JordanAceto/angelo_modular/pcb_docs/dual_ADSR/dual_ADSR_carrier_board/construction_docs/dual_ADSR_schematic.pdf

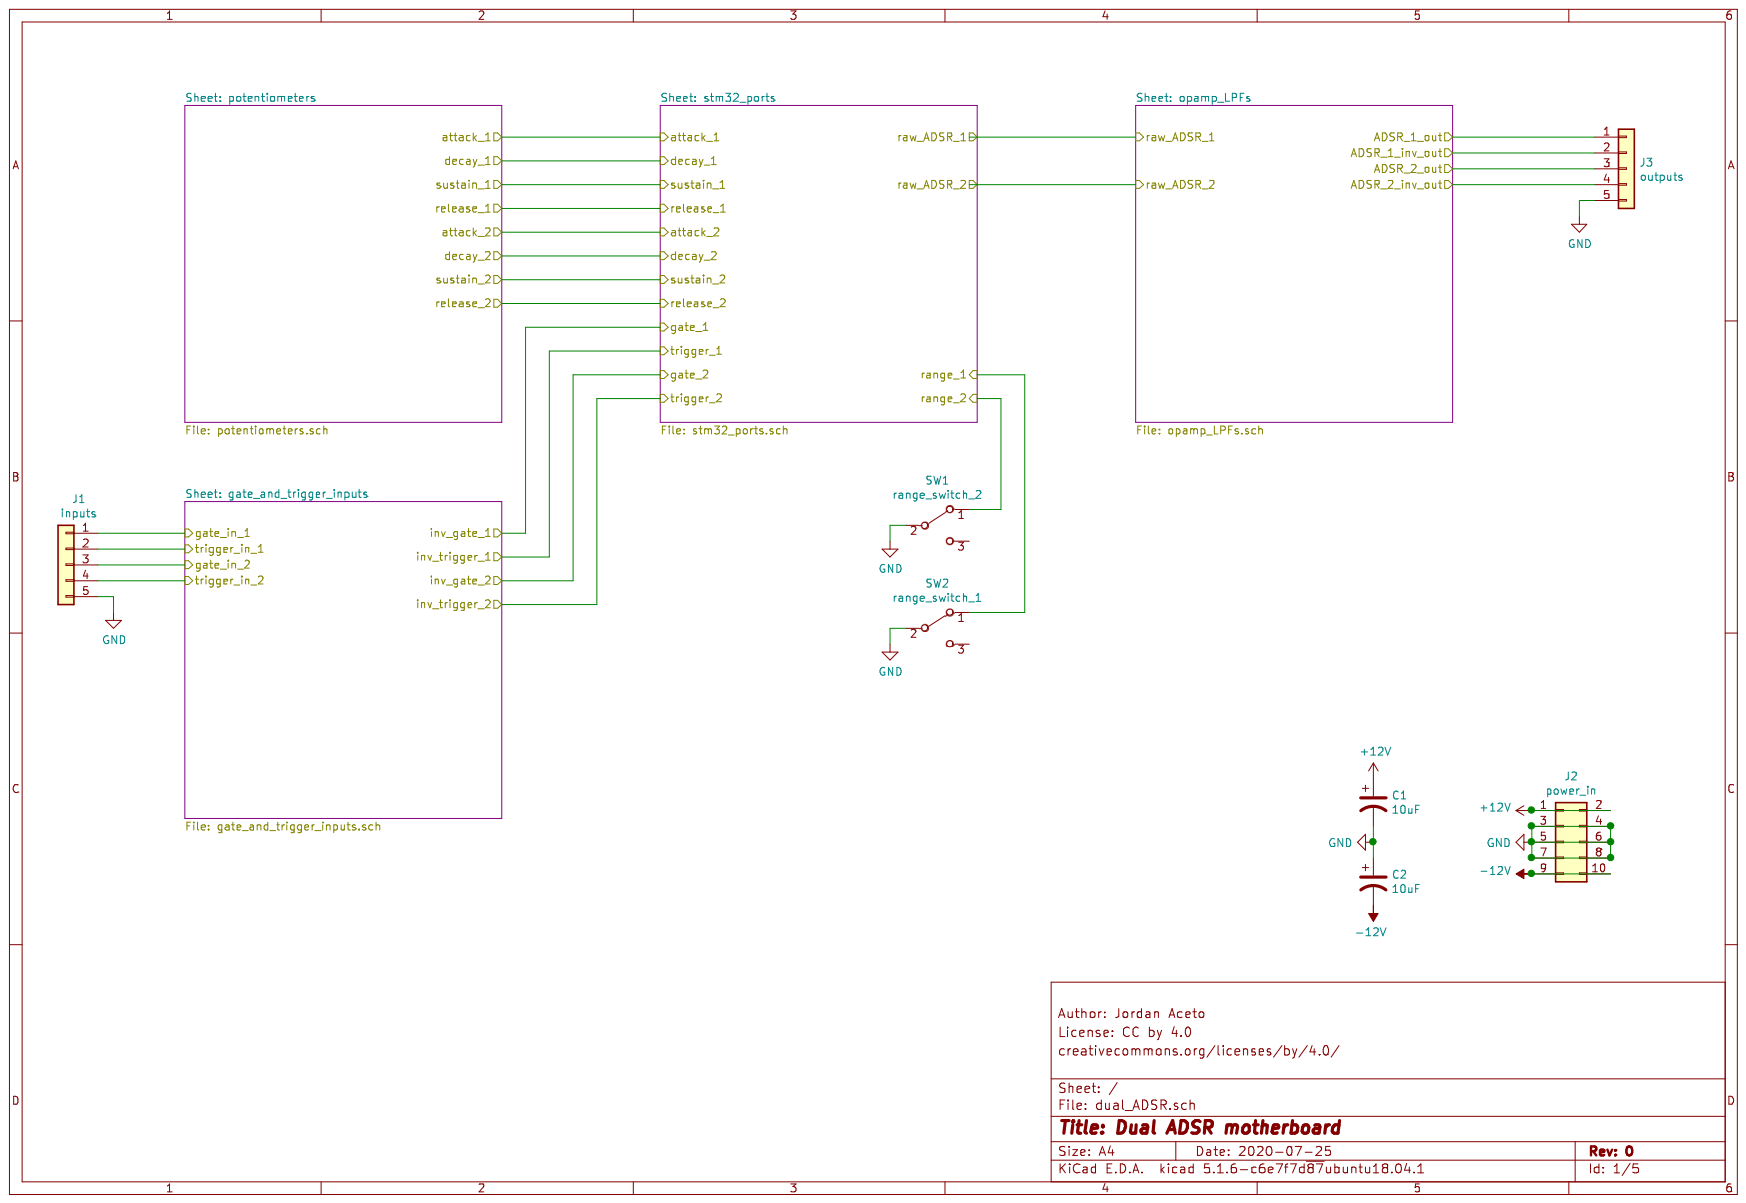
[picture p83: page 1]

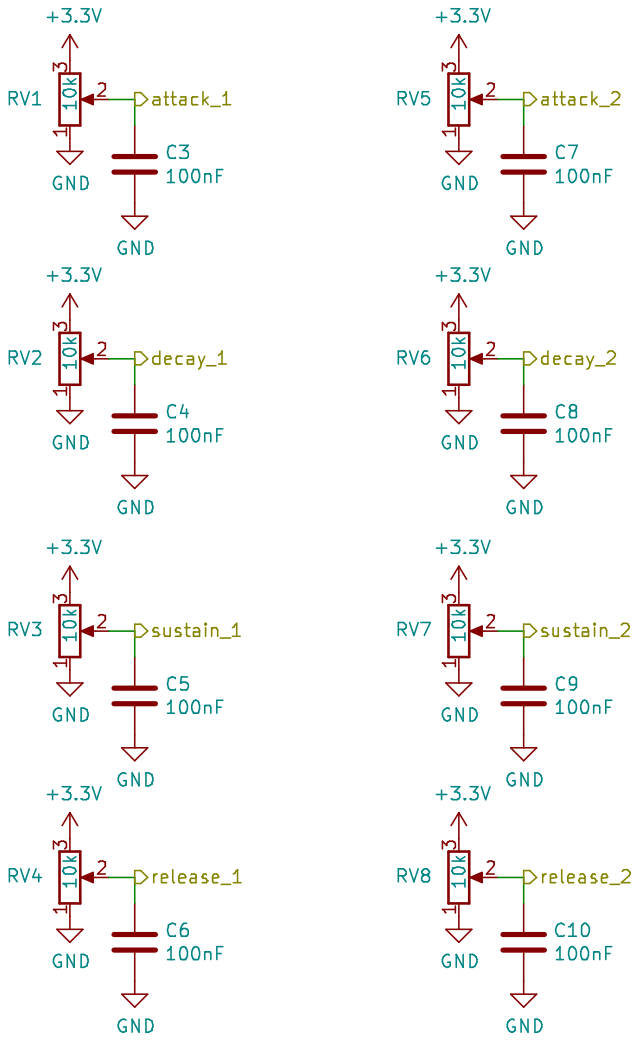
[picture p84: page 2]

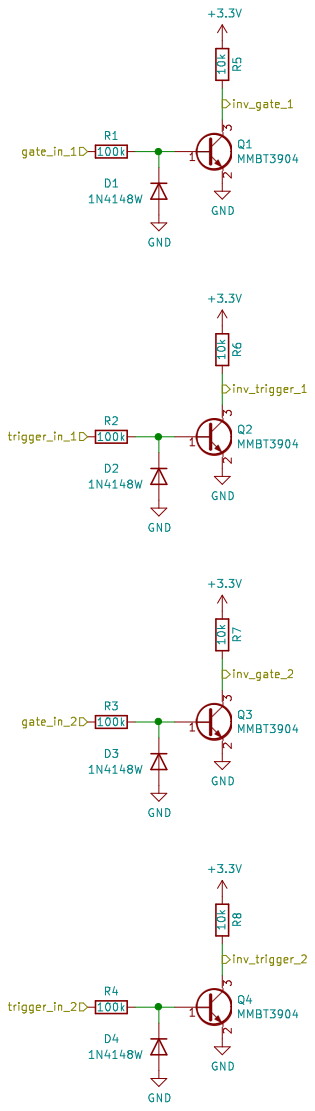
[picture p85: page 3]

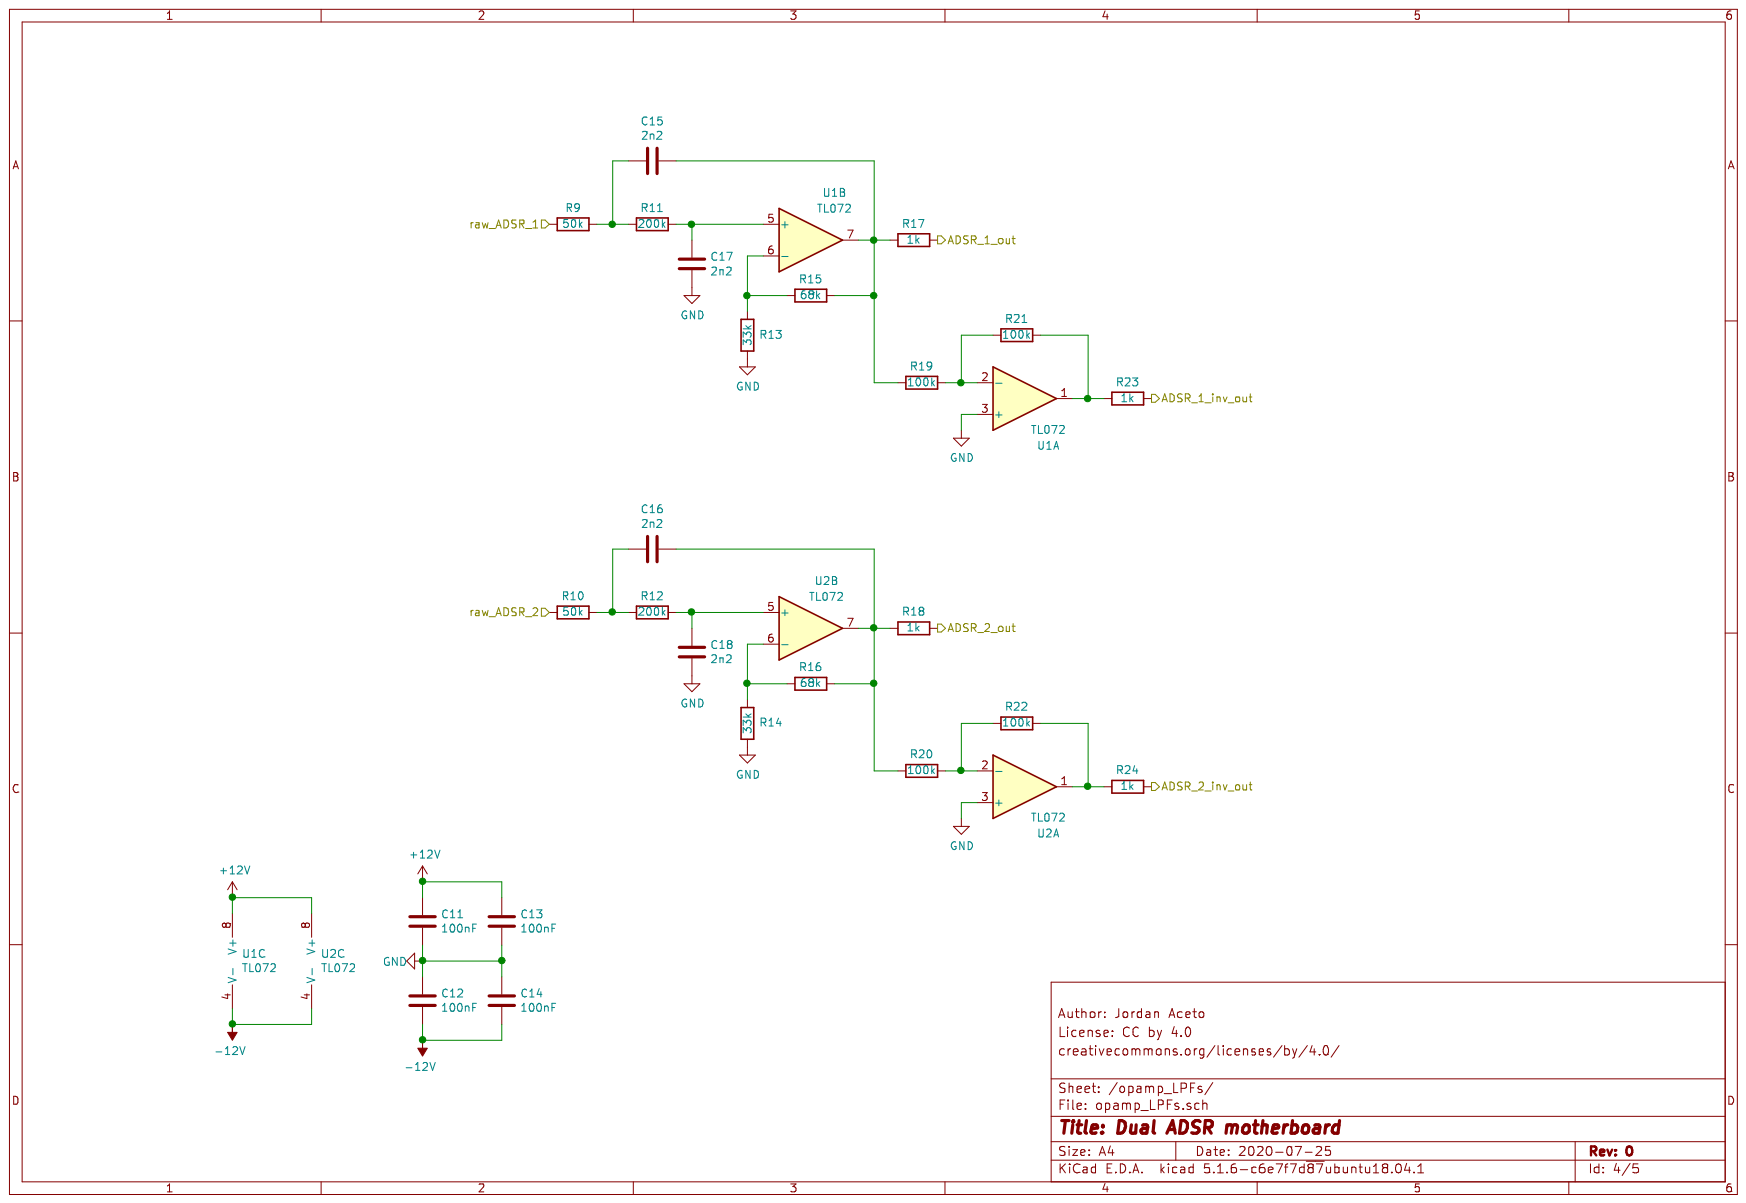
[picture p86: page 4]

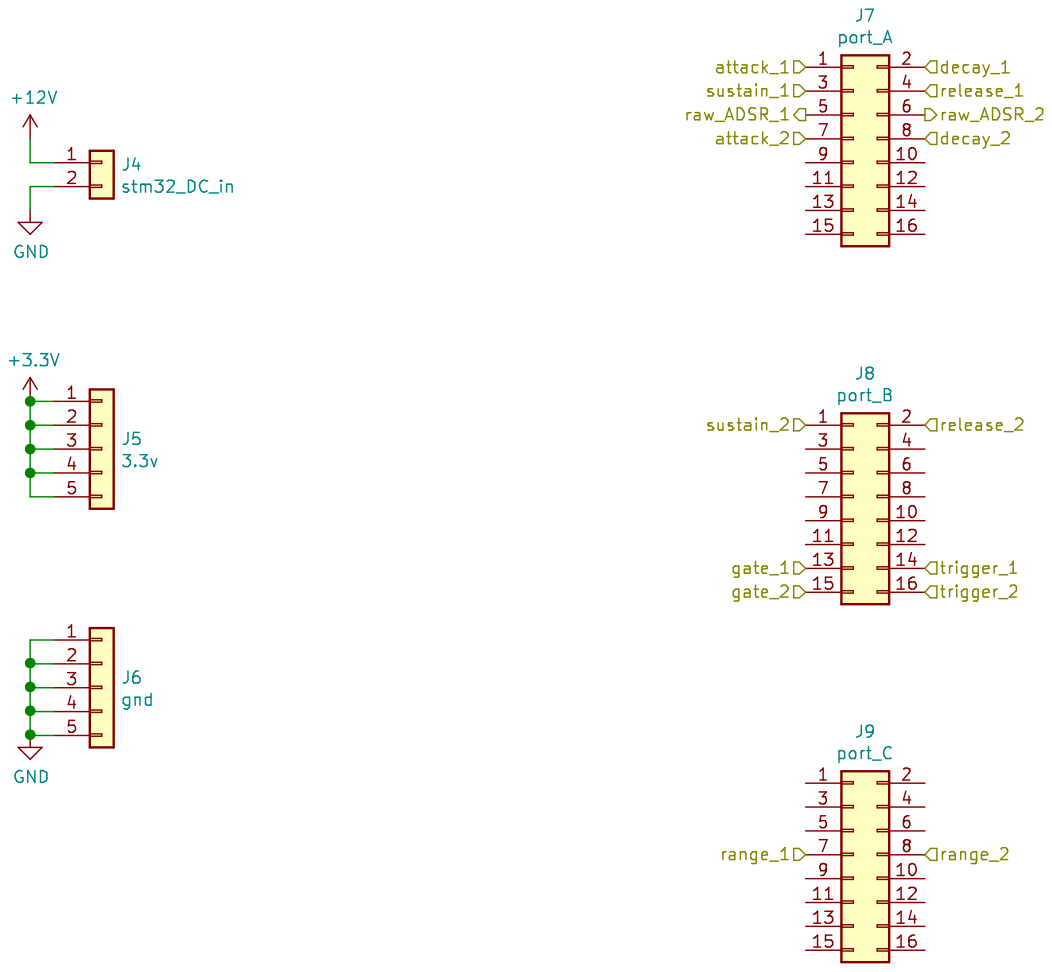
[picture p87: page 5]
