JordanAceto/angelo_modular/pcb_docs/dual_ADSR/STM32F405RGT6_breakout_board/construction_docs/stm32f405_breakout_schematic.pdf

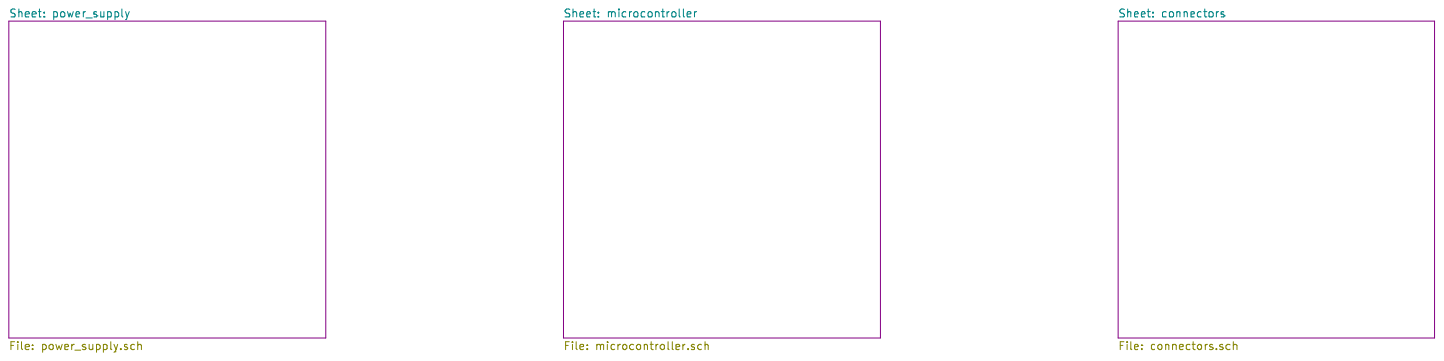
[picture p88: page 1]

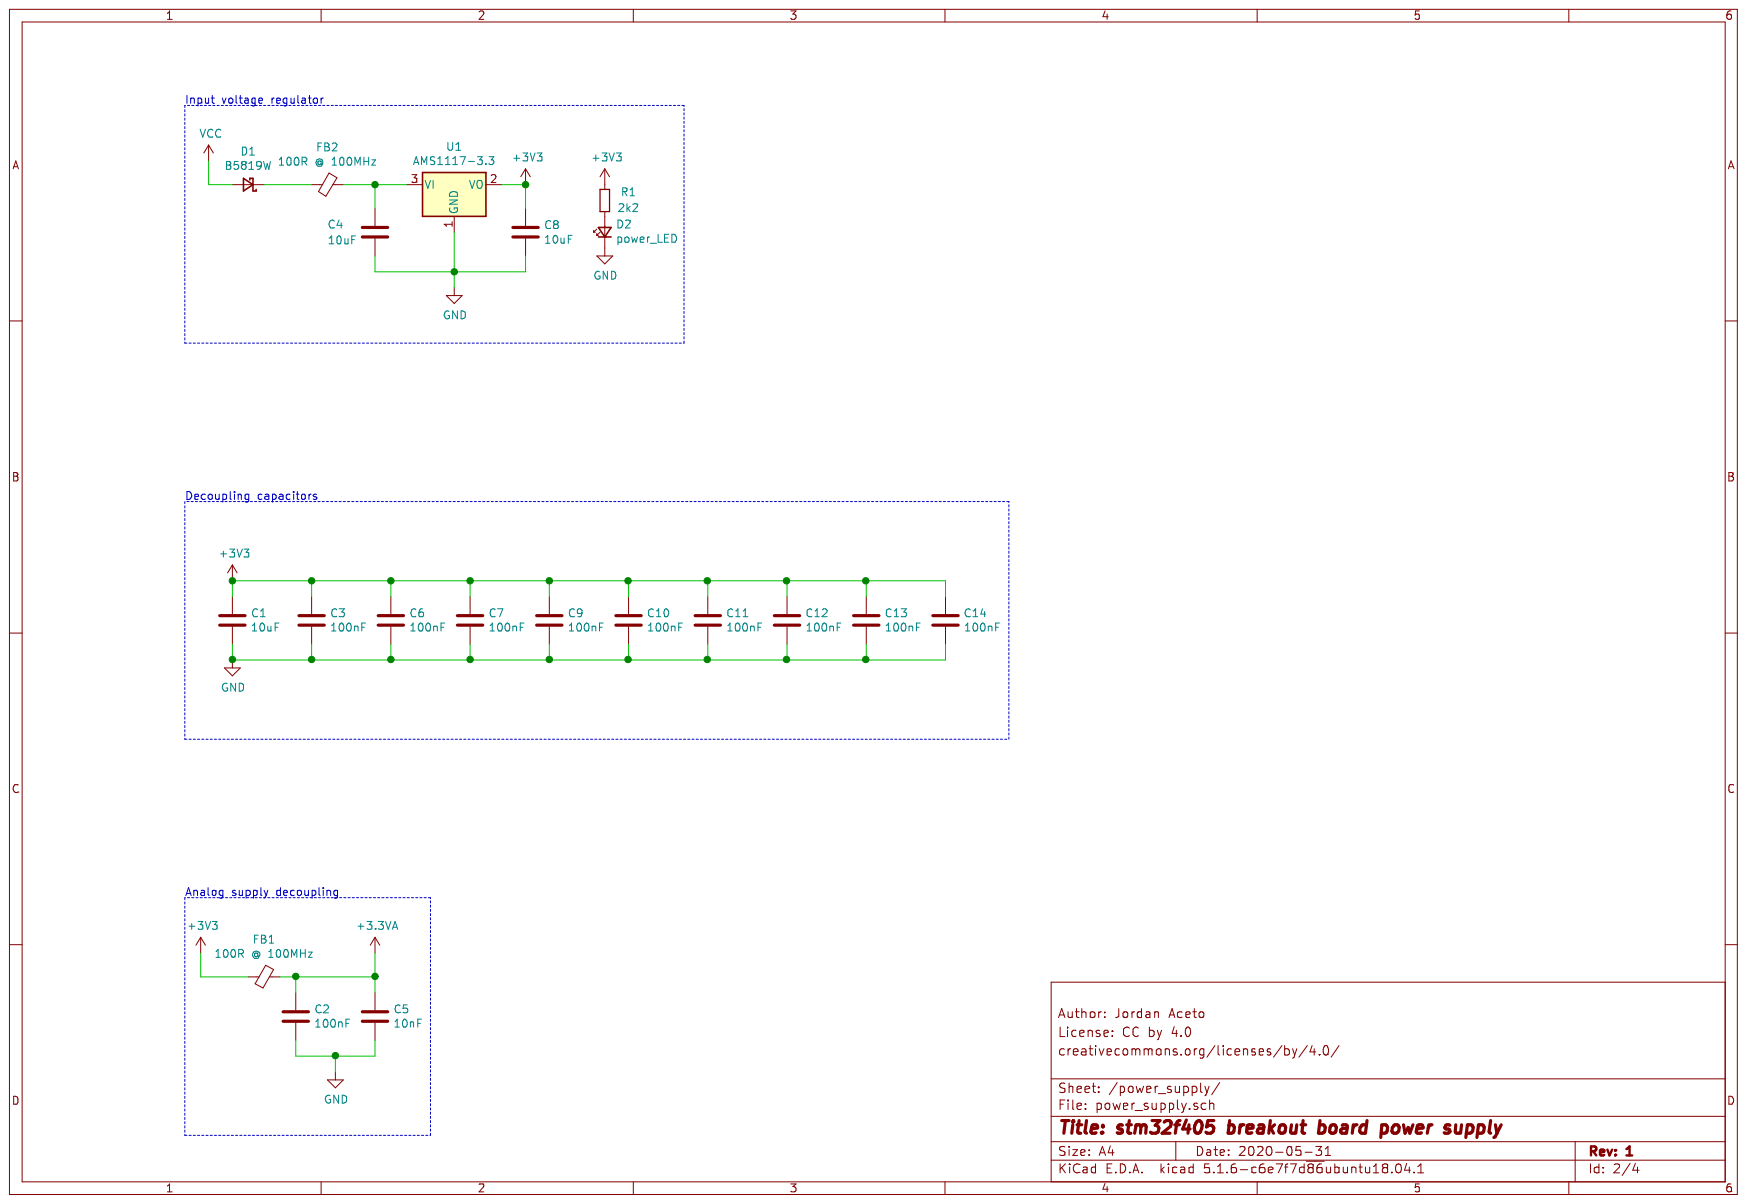
[picture p89: page 2]

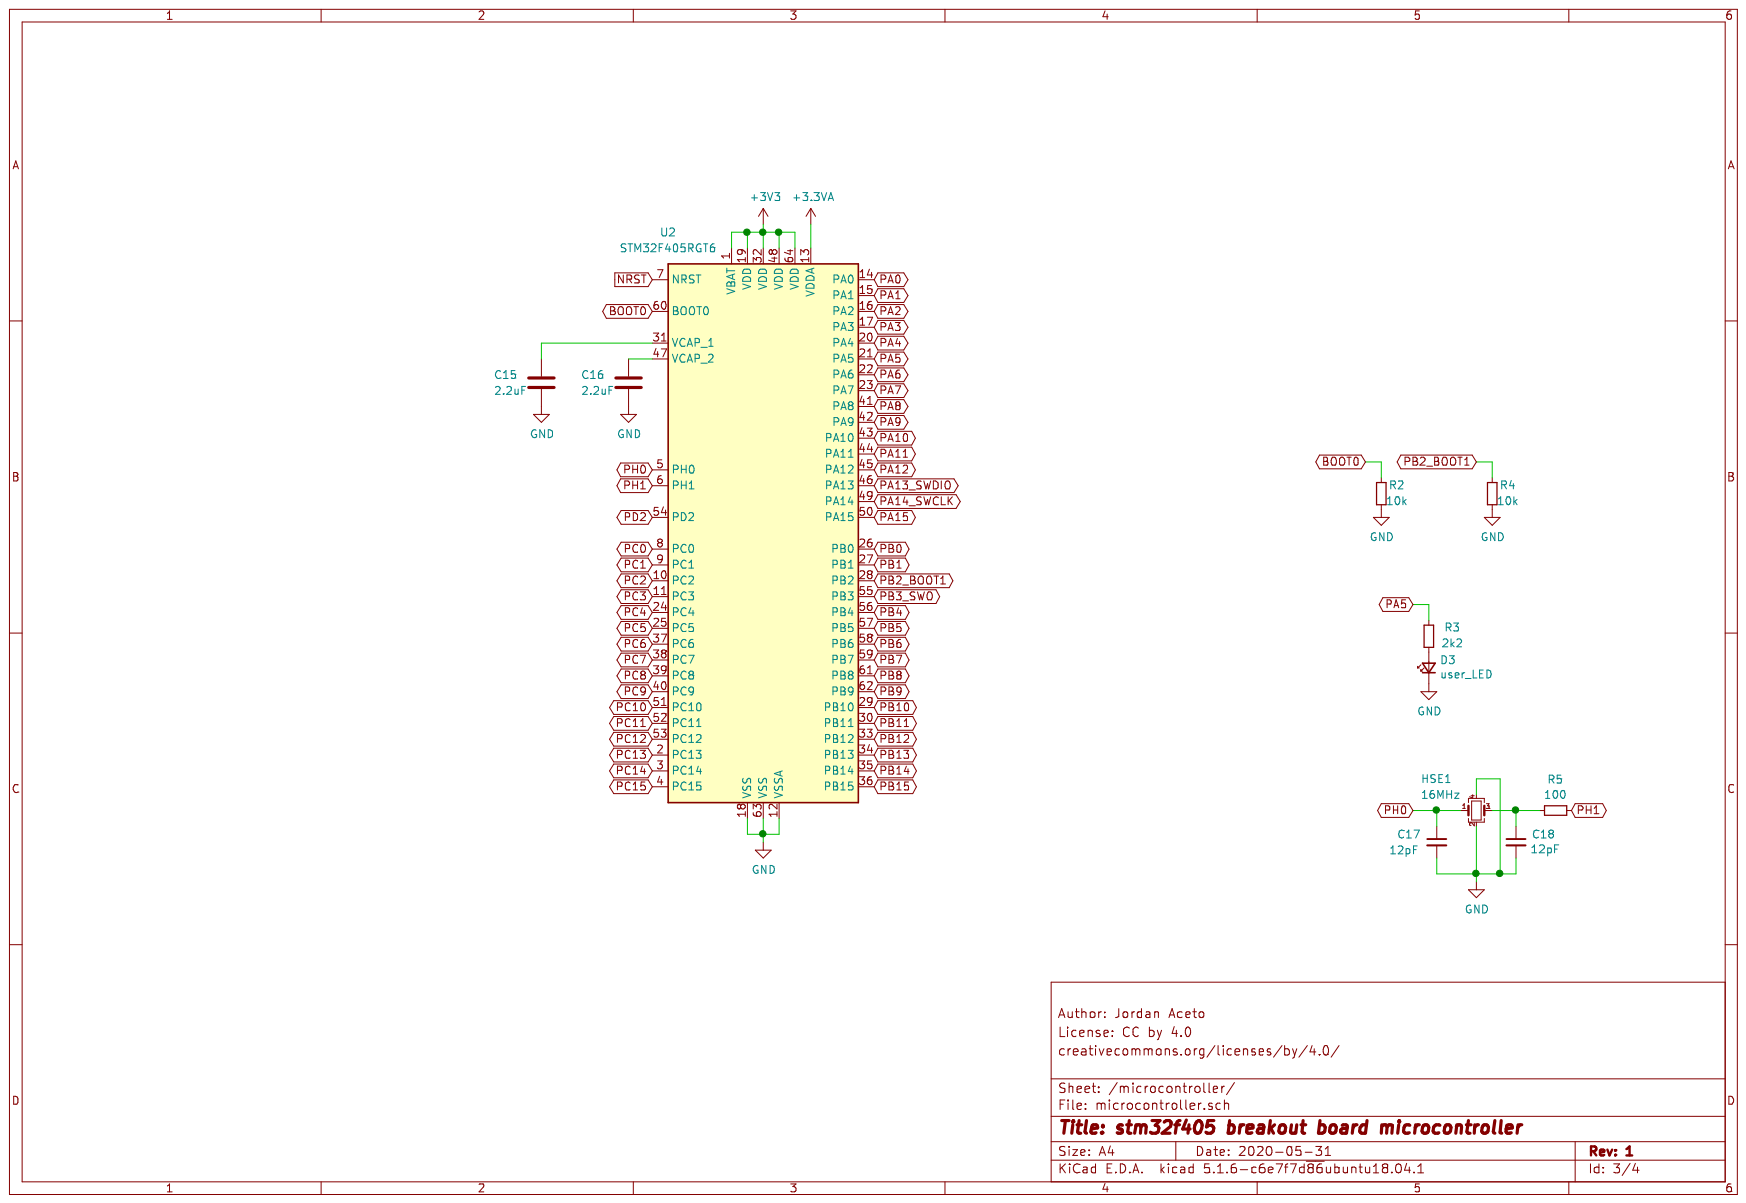
[picture p90: page 3]

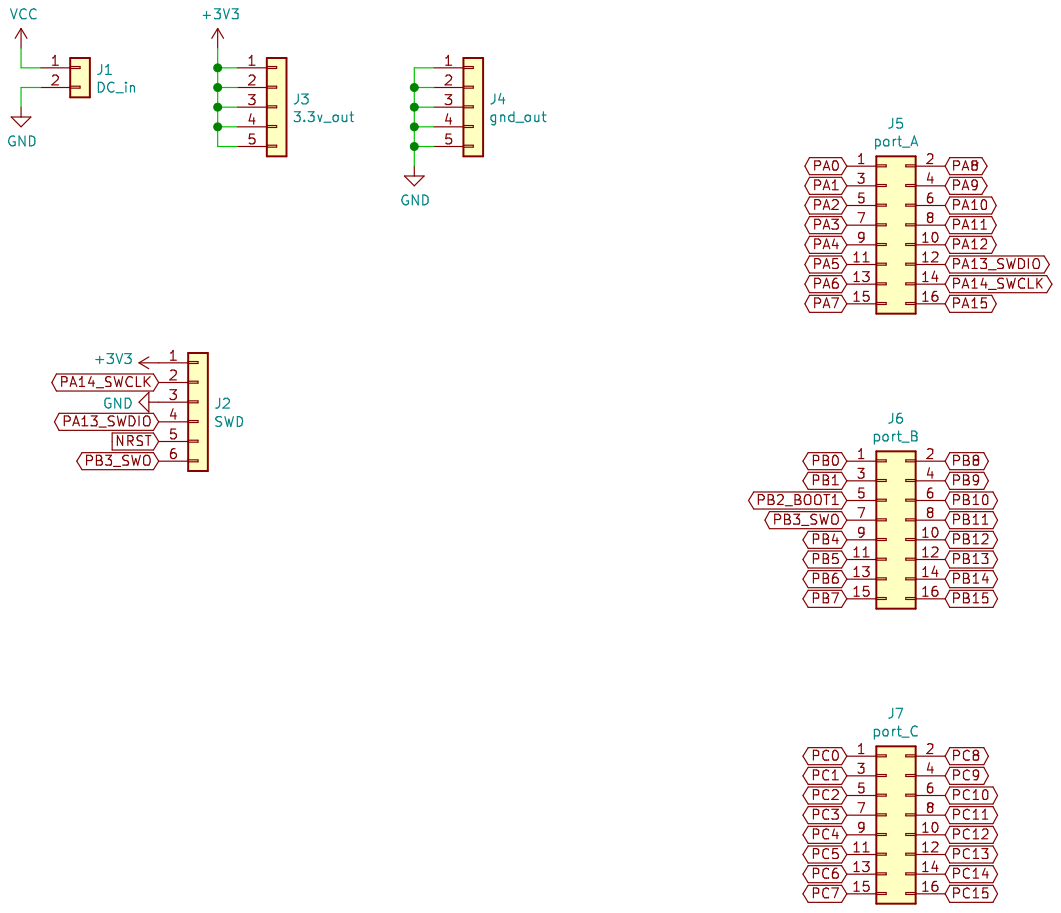
[picture p91: page 4]
