JordanAceto/angelo_modular/pcb_docs/dual_ADSR/STM32F405RGT6_breakout_board/kicad_docs/f405_breakout.kicad_pcb

## KiCad design pcb_docs/dual_ADSR/STM32F405RGT6_breakout_board/kicad_docs/f405_breakout.kicad_pcb (2020-06-21)

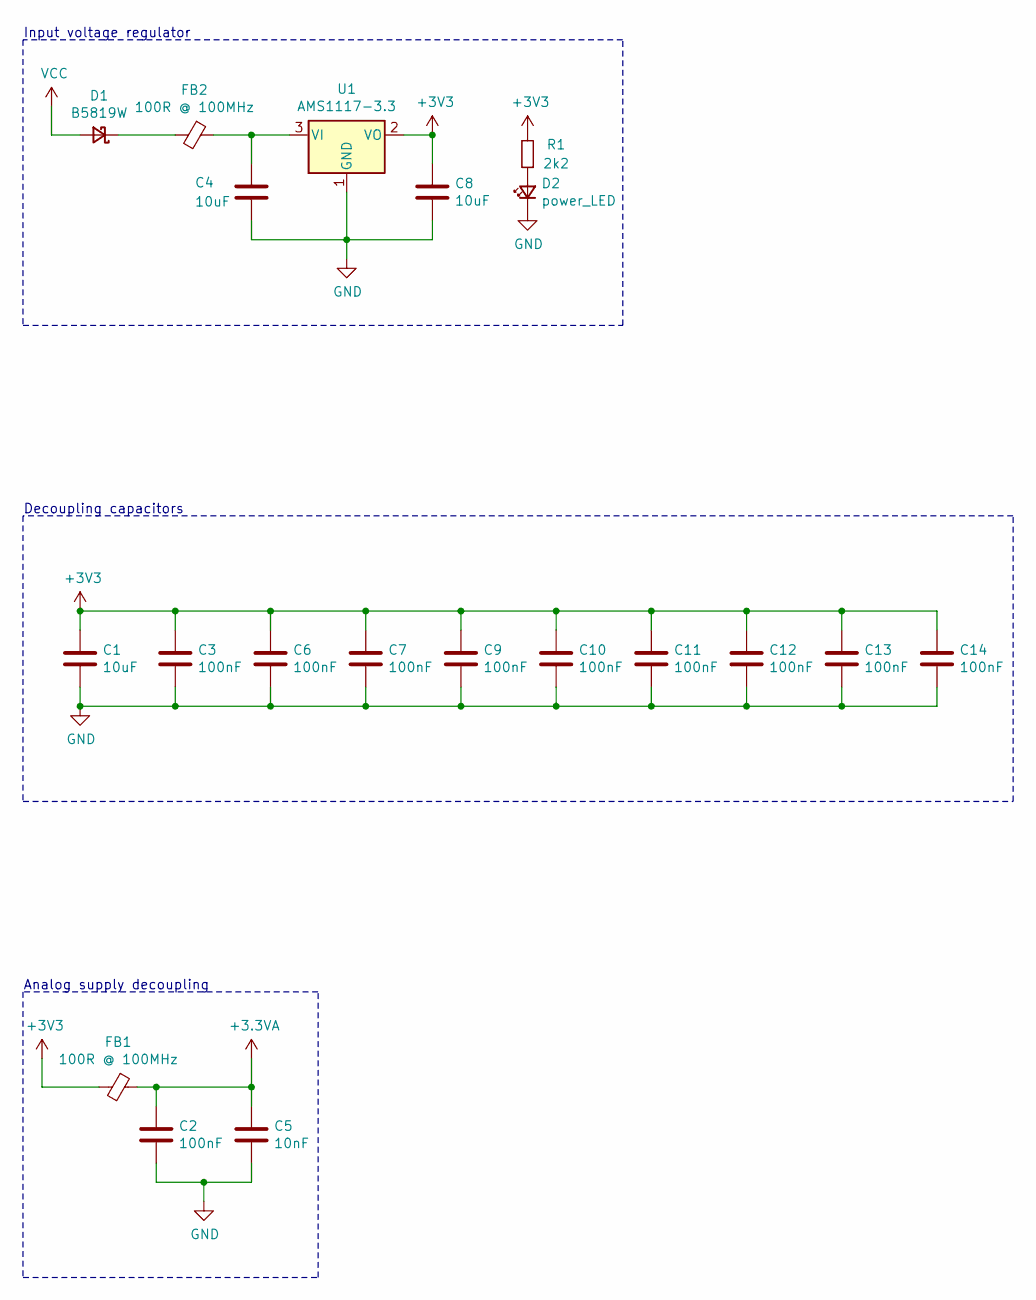
[picture p149: schematic power_supply.sch]

Parts:
C1, C4, C8: 10uF; C_0805_2012Metric
C2, C3, C6, C7, C9, C10, C11, C12, C13, C14: 100nF; C_0402_1005Metric
C5: 10nF; C_0402_1005Metric
D1: B5819W; D_SOD-123
D2: power_LED; LED_0603_1608Metric
FB1, FB2: 100R @ 100MHz; L_0805_2012Metric
R1: 2k2; R_0603_1608Metric
U1: AMS1117-3.3; SOT-223-3_TabPin2

Connections:
+3.3VA: C2.1, C5.1, FB1.1; also elsewhere on the board
+3V3: C1.1, C3.1, C6.1, C7.1, C8.1, C9.1, C10.1, C11.1, C12.1, C13.1, C14.1, FB1.2, R1.2, U1.2 (VO); also elsewhere on the board
GND: C1.2, C2.2, C3.2, C4.2, C5.2, C6.2, C7.2, C8.2, C9.2, C10.2, C11.2, C12.2, C13.2, C14.2, D2.1 (K), U1.1 (GND); also elsewhere on the board
unnamed: C4.1, FB2.1, U1.3 (VI)
unnamed: D1.1 (K), FB2.2
unnamed: D2.2 (A), R1.1
VCC: D1.2 (A); also elsewhere on the board

Notes on the sheet:
Input voltage regulator
Decoupling capacitors
Analog supply decoupling
