JordanAceto/angelo_modular/pcb_docs/dual_ADSR/STM32F405RGT6_breakout_board/kicad_docs/f405_breakout.kicad_pcb

## KiCad design pcb_docs/dual_ADSR/STM32F405RGT6_breakout_board/kicad_docs/f405_breakout.kicad_pcb (continued)

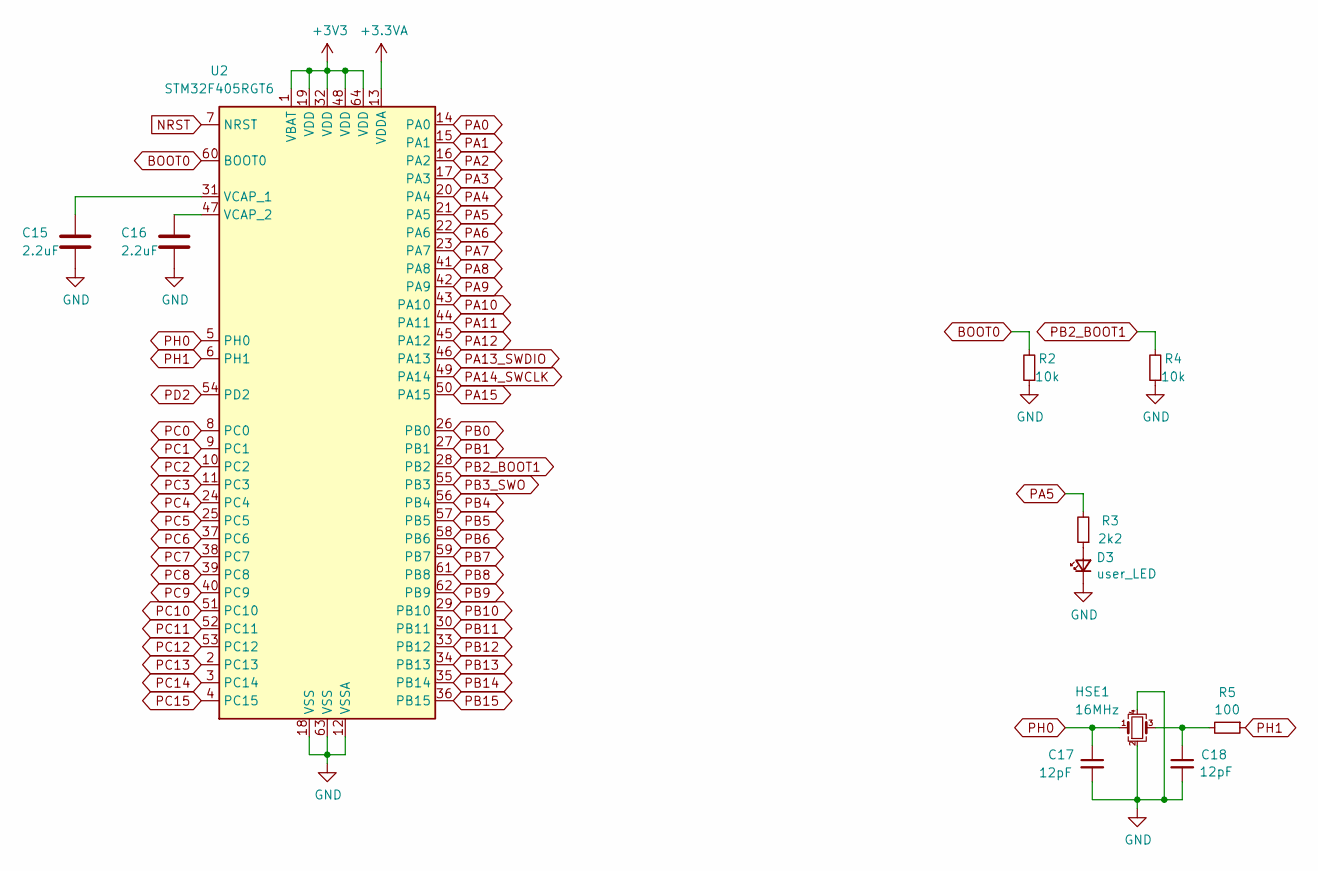
[picture p150: schematic microcontroller.sch]

Parts:
C15, C16: 2.2uF; C_0603_1608Metric
C17, C18: 12pF; C_0402_1005Metric
D3: user_LED; LED_0603_1608Metric
HSE1: 16MHz; Crystal_SMD_3225-4Pin_3.2x2.5mm
R2, R4: 10k; R_0402_1005Metric
R3: 2k2; R_0603_1608Metric
R5: 100; R_0402_1005Metric
U2: STM32F405RGT6; LQFP-64_10x10mm_P0.5mm

Connections:
+3.3VA: U2.13 (VDDA); also elsewhere on the board
+3V3: U2.1 (VBAT), U2.19 (VDD), U2.32 (VDD), U2.48 (VDD), U2.64 (VDD); also elsewhere on the board
BOOT0: R2.2, U2.60 (BOOT0)
GND: C15.2, C16.2, C17.2, C18.2, D3.1 (K), HSE1.2, HSE1.4, R2.1, R4.1, U2.12 (VSSA), U2.18 (VSS), U2.63 (VSS); also elsewhere on the board
NRST: U2.7 (NRST); also elsewhere on the board
unnamed: C15.1, U2.31 (VCAP_1)
unnamed: C16.1, U2.47 (VCAP_2)
unnamed: C18.1, HSE1.3, R5.2
unnamed: D3.2 (A), R3.1
PA0: U2.14 (PA0); also elsewhere on the board
PA1: U2.15 (PA1); also elsewhere on the board
PA2: U2.16 (PA2); also elsewhere on the board
PA3: U2.17 (PA3); also elsewhere on the board
PA4: U2.20 (PA4); also elsewhere on the board
PA5: R3.2, U2.21 (PA5); also elsewhere on the board
PA6: U2.22 (PA6); also elsewhere on the board
PA7: U2.23 (PA7); also elsewhere on the board
PA8: U2.41 (PA8); also elsewhere on the board
PA9: U2.42 (PA9); also elsewhere on the board
PA10: U2.43 (PA10); also elsewhere on the board
PA11: U2.44 (PA11); also elsewhere on the board
PA12: U2.45 (PA12); also elsewhere on the board
PA13_SWDIO: U2.46 (PA13); also elsewhere on the board
PA14_SWCLK: U2.49 (PA14); also elsewhere on the board
PA15: U2.50 (PA15); also elsewhere on the board
PB0: U2.26 (PB0); also elsewhere on the board
PB1: U2.27 (PB1); also elsewhere on the board
PB2_BOOT1: R4.2, U2.28 (PB2); also elsewhere on the board
PB3_SWO: U2.55 (PB3); also elsewhere on the board
PB4: U2.56 (PB4); also elsewhere on the board
PB5: U2.57 (PB5); also elsewhere on the board
PB6: U2.58 (PB6); also elsewhere on the board
PB7: U2.59 (PB7); also elsewhere on the board
PB8: U2.61 (PB8); also elsewhere on the board
PB9: U2.62 (PB9); also elsewhere on the board
PB10: U2.29 (PB10); also elsewhere on the board
PB11: U2.30 (PB11); also elsewhere on the board
PB12: U2.33 (PB12); also elsewhere on the board
PB13: U2.34 (PB13); also elsewhere on the board
PB14: U2.35 (PB14); also elsewhere on the board
PB15: U2.36 (PB15); also elsewhere on the board
PC0: U2.8 (PC0); also elsewhere on the board
PC1: U2.9 (PC1); also elsewhere on the board
PC2: U2.10 (PC2); also elsewhere on the board
PC3: U2.11 (PC3); also elsewhere on the board
PC4: U2.24 (PC4); also elsewhere on the board
PC5: U2.25 (PC5); also elsewhere on the board
PC6: U2.37 (PC6); also elsewhere on the board
PC7: U2.38 (PC7); also elsewhere on the board
PC8: U2.39 (PC8); also elsewhere on the board
PC9: U2.40 (PC9); also elsewhere on the board
PC10: U2.51 (PC10); also elsewhere on the board
PC11: U2.52 (PC11); also elsewhere on the board
PC12: U2.53 (PC12); also elsewhere on the board
PC13: U2.2 (PC13); also elsewhere on the board
PC14: U2.3 (PC14); also elsewhere on the board
PC15: U2.4 (PC15); also elsewhere on the board
PD2: U2.54 (PD2)
PH0: C17.1, HSE1.1, U2.5 (PH0)
PH1: R5.1, U2.6 (PH1)

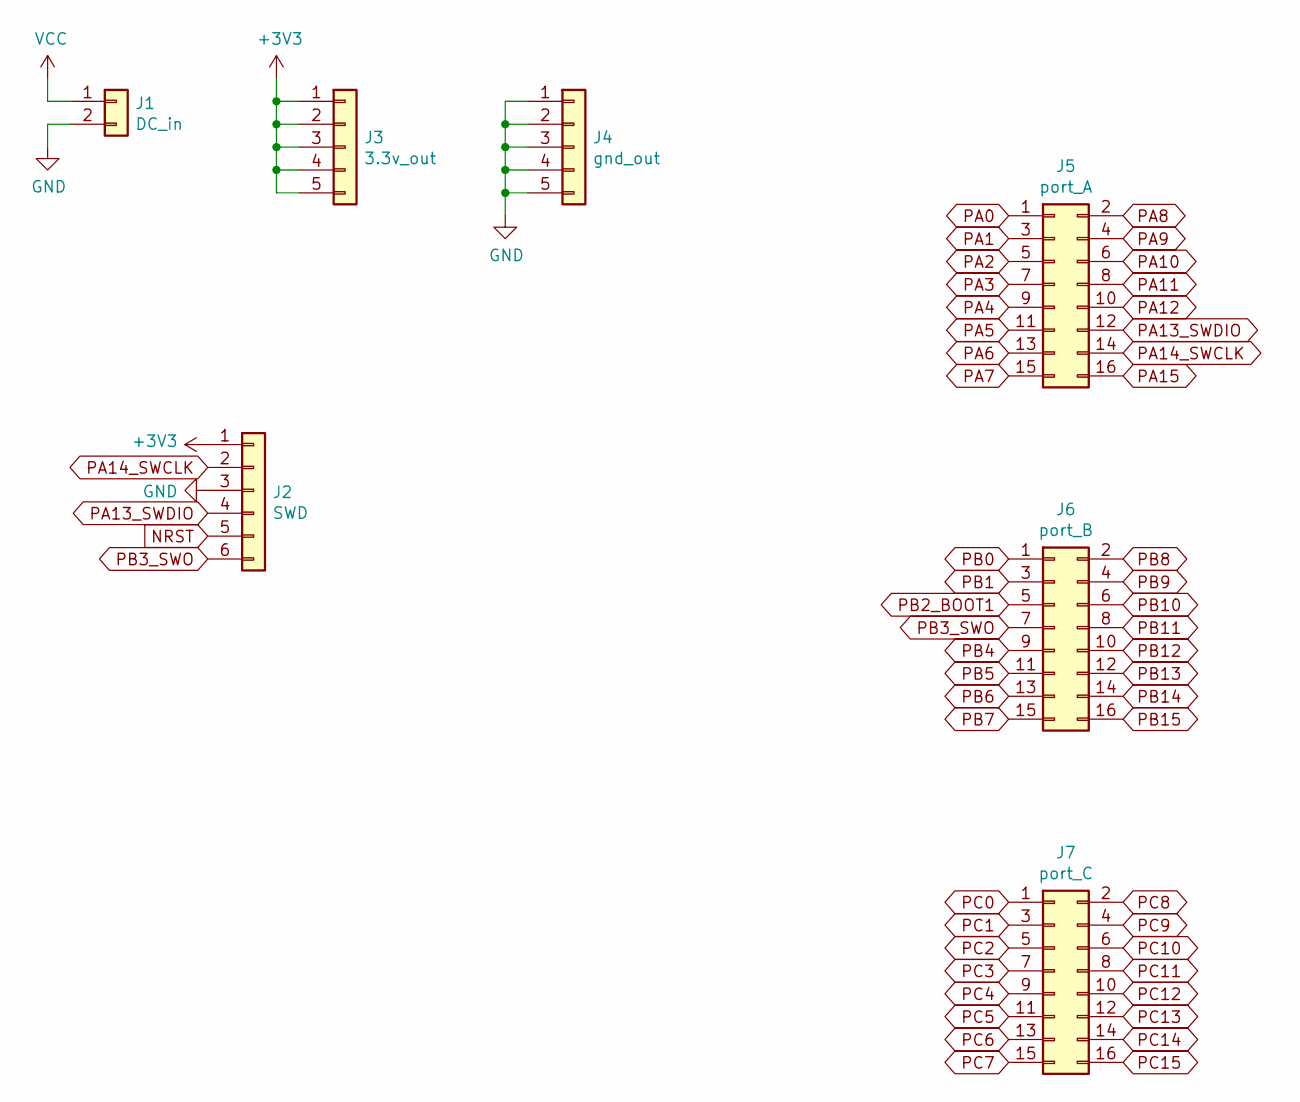
[picture p151: schematic connectors.sch]

Parts:
J1: DC_in; PinSocket_1x02_P2.54mm_Vertical
J2: SWD; PinSocket_1x06_P2.54mm_Vertical
J3: 3.3v_out; PinSocket_1x05_P2.54mm_Vertical
J4: gnd_out; PinSocket_1x05_P2.54mm_Vertical
J5: port_A; PinHeader_2x08_P2.54mm_Vertical
J6: port_B; PinHeader_2x08_P2.54mm_Vertical
J7: port_C; PinHeader_2x08_P2.54mm_Vertical

Connections:
+3V3: J2.1, J3.1, J3.2, J3.3, J3.4, J3.5; also elsewhere on the board
GND: J1.2, J2.3, J4.1, J4.2, J4.3, J4.4, J4.5; also elsewhere on the board
NRST: J2.5; also elsewhere on the board
PA0: J5.1; also elsewhere on the board
PA1: J5.3; also elsewhere on the board
PA2: J5.5; also elsewhere on the board
PA3: J5.7; also elsewhere on the board
PA4: J5.9; also elsewhere on the board
PA5: J5.11; also elsewhere on the board
PA6: J5.13; also elsewhere on the board
PA7: J5.15; also elsewhere on the board
PA8: J5.2; also elsewhere on the board
PA9: J5.4; also elsewhere on the board
PA10: J5.6; also elsewhere on the board
PA11: J5.8; also elsewhere on the board
PA12: J5.10; also elsewhere on the board
PA13_SWDIO: J2.4, J5.12; also elsewhere on the board
PA14_SWCLK: J2.2, J5.14; also elsewhere on the board
PA15: J5.16; also elsewhere on the board
PB0: J6.1; also elsewhere on the board
PB1: J6.3; also elsewhere on the board
PB2_BOOT1: J6.5; also elsewhere on the board
PB3_SWO: J2.6, J6.7; also elsewhere on the board
PB4: J6.9; also elsewhere on the board
PB5: J6.11; also elsewhere on the board
PB6: J6.13; also elsewhere on the board
PB7: J6.15; also elsewhere on the board
PB8: J6.2; also elsewhere on the board
PB9: J6.4; also elsewhere on the board
PB10: J6.6; also elsewhere on the board
PB11: J6.8; also elsewhere on the board
PB12: J6.10; also elsewhere on the board
PB13: J6.12; also elsewhere on the board
PB14: J6.14; also elsewhere on the board
PB15: J6.16; also elsewhere on the board
PC0: J7.1; also elsewhere on the board
PC1: J7.3; also elsewhere on the board
PC2: J7.5; also elsewhere on the board
PC3: J7.7; also elsewhere on the board
PC4: J7.9; also elsewhere on the board
PC5: J7.11; also elsewhere on the board
PC6: J7.13; also elsewhere on the board
PC7: J7.15; also elsewhere on the board
PC8: J7.2; also elsewhere on the board
PC9: J7.4; also elsewhere on the board
PC10: J7.6; also elsewhere on the board
PC11: J7.8; also elsewhere on the board
PC12: J7.10; also elsewhere on the board
PC13: J7.12; also elsewhere on the board
PC14: J7.14; also elsewhere on the board
PC15: J7.16; also elsewhere on the board
VCC: J1.1; also elsewhere on the board

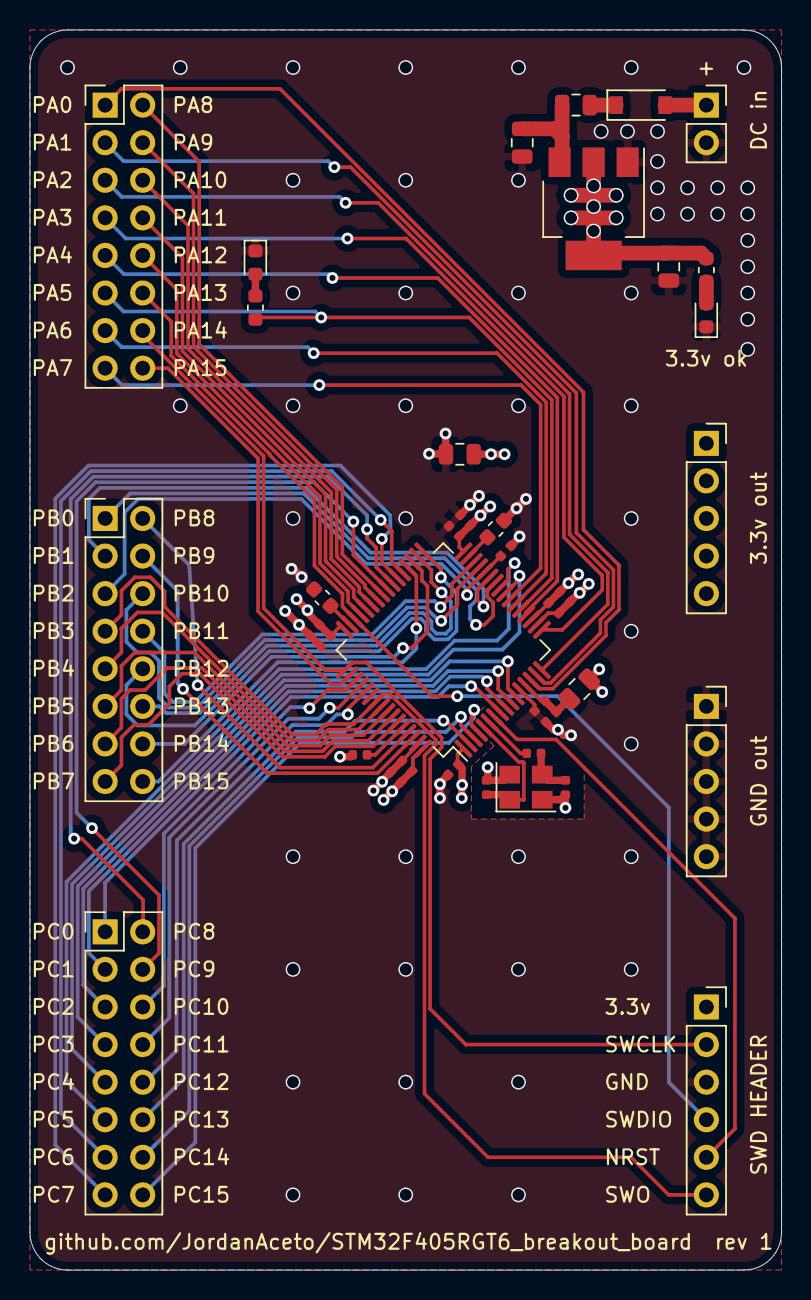
[picture p152: board f405_breakout.kicad_pcb from above]

Board: 4 copper layers, 50.8 x 83.8 mm, 38 parts (0 on the bottom side), 63 nets.
