JordanAceto/angelo_modular/pcb_docs/CEM3340_VCO/kicad_docs/CEM3340_VCO.kicad_pcb

## KiCad design pcb_docs/CEM3340_VCO/kicad_docs/CEM3340_VCO.kicad_pcb (2020-06-26)

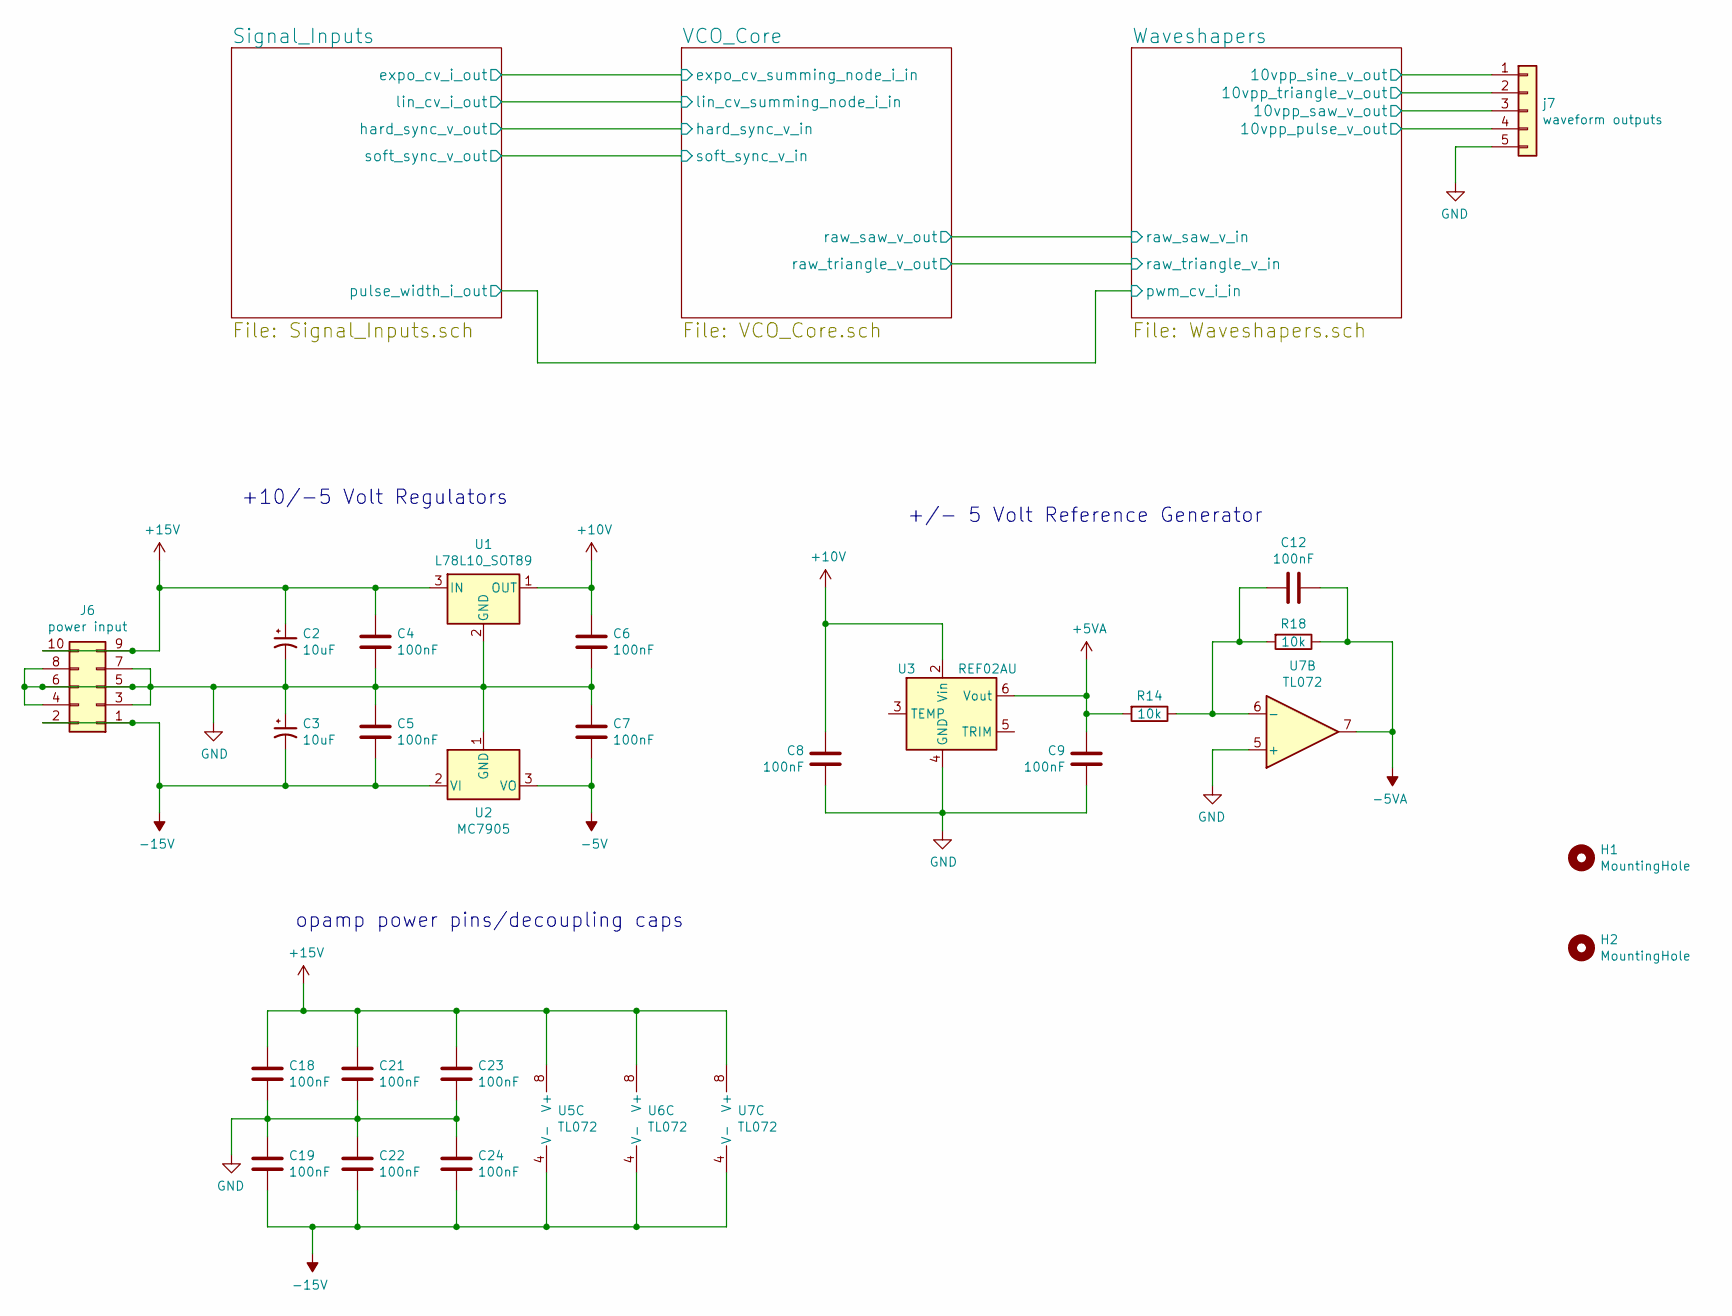
[picture p153: schematic CEM3340_VCO.sch, CEM3340 VCO]

Parts:
C2, C3: 10uF; CP_Elec_5x5.4
C4, C5, C6, C7, C8, C9, C12, C18, C19, C21, C22, C23, C24: 100nF; C_0805_2012Metric_Pad1.15x1.40mm_HandSolder
H1, H2: MountingHole; MountingHole_3.2mm_M3
J6: power input; PinHeader_2x05_P2.54mm_Vertical
R14, R18: 10k; R_0805_2012Metric_Pad1.15x1.40mm_HandSolder
U1: L78L10_SOT89; SOT-89-3_Handsoldering
U2: MC7905; SOT-89-3_Handsoldering
U3: REF02AU; SOIC-8_3.9x4.9mm_P1.27mm
U5, U6, U7: TL072; SOIC-8_3.9x4.9mm_P1.27mm
j7: waveform outputs; PinHeader_1x05_P2.54mm_Vertical

Connections:
+5VA: C9.2, R14.2, U3.6 (Vout); also elsewhere on the board
+10V: C6.2, C8.2, U1.1 (OUT), U3.2 (Vin); also elsewhere on the board
+15V: C2.1, C4.1, C18.1, C21.1, C23.1, J6.9, J6.10, U1.3 (IN), U5.8 (V+), U6.8 (V+), U7.8 (V+); also elsewhere on the board
-5V: C7.1, U2.3 (VO); also elsewhere on the board
-5VA: C12.1, R18.1, U7.7; also elsewhere on the board
-15V: C3.2, C5.2, C19.2, C22.2, C24.2, J6.1, J6.2, U2.2 (VI), U5.4 (V-), U6.4 (V-), U7.4 (V-); also elsewhere on the board
/Waveshapers/10vpp_pulse_v_out: j7.4; also elsewhere on the board
/Waveshapers/10vpp_saw_v_out: j7.3; also elsewhere on the board
/Waveshapers/10vpp_sine_v_out: j7.1; also elsewhere on the board
/Waveshapers/10vpp_triangle_v_out: j7.2; also elsewhere on the board
GND: C2.2, C3.1, C4.2, C5.1, C6.1, C7.2, C8.1, C9.1, C18.2, C19.1, C21.2, C22.1, C23.2, C24.1, J6.3, J6.4, J6.5, J6.6, J6.7, J6.8, U1.2 (GND), U2.1 (GND), U3.4 (GND), U7.5 (+), j7.5; also elsewhere on the board
unnamed: C12.2, R14.1, R18.2, U7.6 (-)

Notes on the sheet:
+/- 5 Volt Reference Generator
+10/-5 Volt Regulators
opamp power pins/decoupling caps

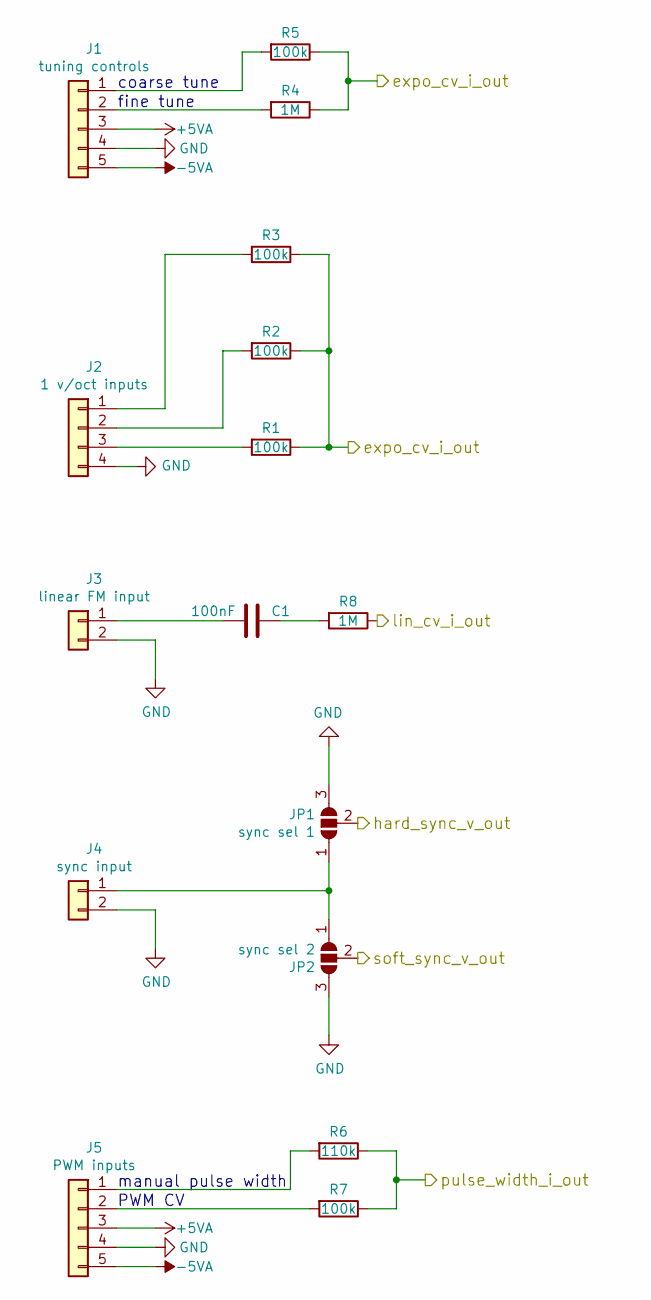
[picture p154: schematic Signal_Inputs.sch, CEM3340 VCO Signal Inputs]

Parts:
C1: 100nF; C_0805_2012Metric_Pad1.15x1.40mm_HandSolder
J1: tuning controls; PinHeader_1x05_P2.54mm_Vertical
J2: 1 v/oct inputs; PinHeader_1x04_P2.54mm_Vertical
J3: linear FM input; PinHeader_1x02_P2.54mm_Vertical
J4: sync input; PinHeader_1x02_P2.54mm_Vertical
J5: PWM inputs; PinHeader_1x05_P2.54mm_Vertical
JP1: sync sel 1; SolderJumper-3_P1.3mm_Open_RoundedPad1.0x1.5mm
JP2: sync sel 2; SolderJumper-3_P1.3mm_Open_RoundedPad1.0x1.5mm
R1, R2, R3, R5, R7: 100k; R_0805_2012Metric_Pad1.15x1.40mm_HandSolder
R4, R8: 1M; R_0805_2012Metric_Pad1.15x1.40mm_HandSolder
R6: 110k; R_0805_2012Metric_Pad1.15x1.40mm_HandSolder

Connections:
+5VA: J1.3, J5.3; also elsewhere on the board
-5VA: J1.5, J5.5; also elsewhere on the board
/Signal_Inputs/expo_cv_i_out: R1.1, R2.1, R3.1, R4.1, R5.1; also elsewhere on the board
/Signal_Inputs/lin_cv_i_out: R8.1; also elsewhere on the board
/Signal_Inputs/pulse_width_i_out: R6.1, R7.1
/VCO_Core/hard_sync_v_in: JP1.2 (C); also elsewhere on the board
/VCO_Core/soft_sync_v_in: JP2.2 (C); also elsewhere on the board
GND: J1.4, J2.4, J3.2, J4.2, J5.4, JP1.3 (B), JP2.3 (B); also elsewhere on the board
unnamed: C1.1, R8.2
unnamed: C1.2, J3.1
unnamed: J1.1, R5.2
unnamed: J1.2, R4.2
unnamed: J2.1, R3.2
unnamed: J2.2, R2.2
unnamed: J2.3, R1.2
unnamed: J4.1, JP1.1 (A), JP2.1 (A)
unnamed: J5.1, R6.2
unnamed: J5.2, R7.2

Notes on the sheet:
manual pulse width
PWM CV
fine tune
coarse tune

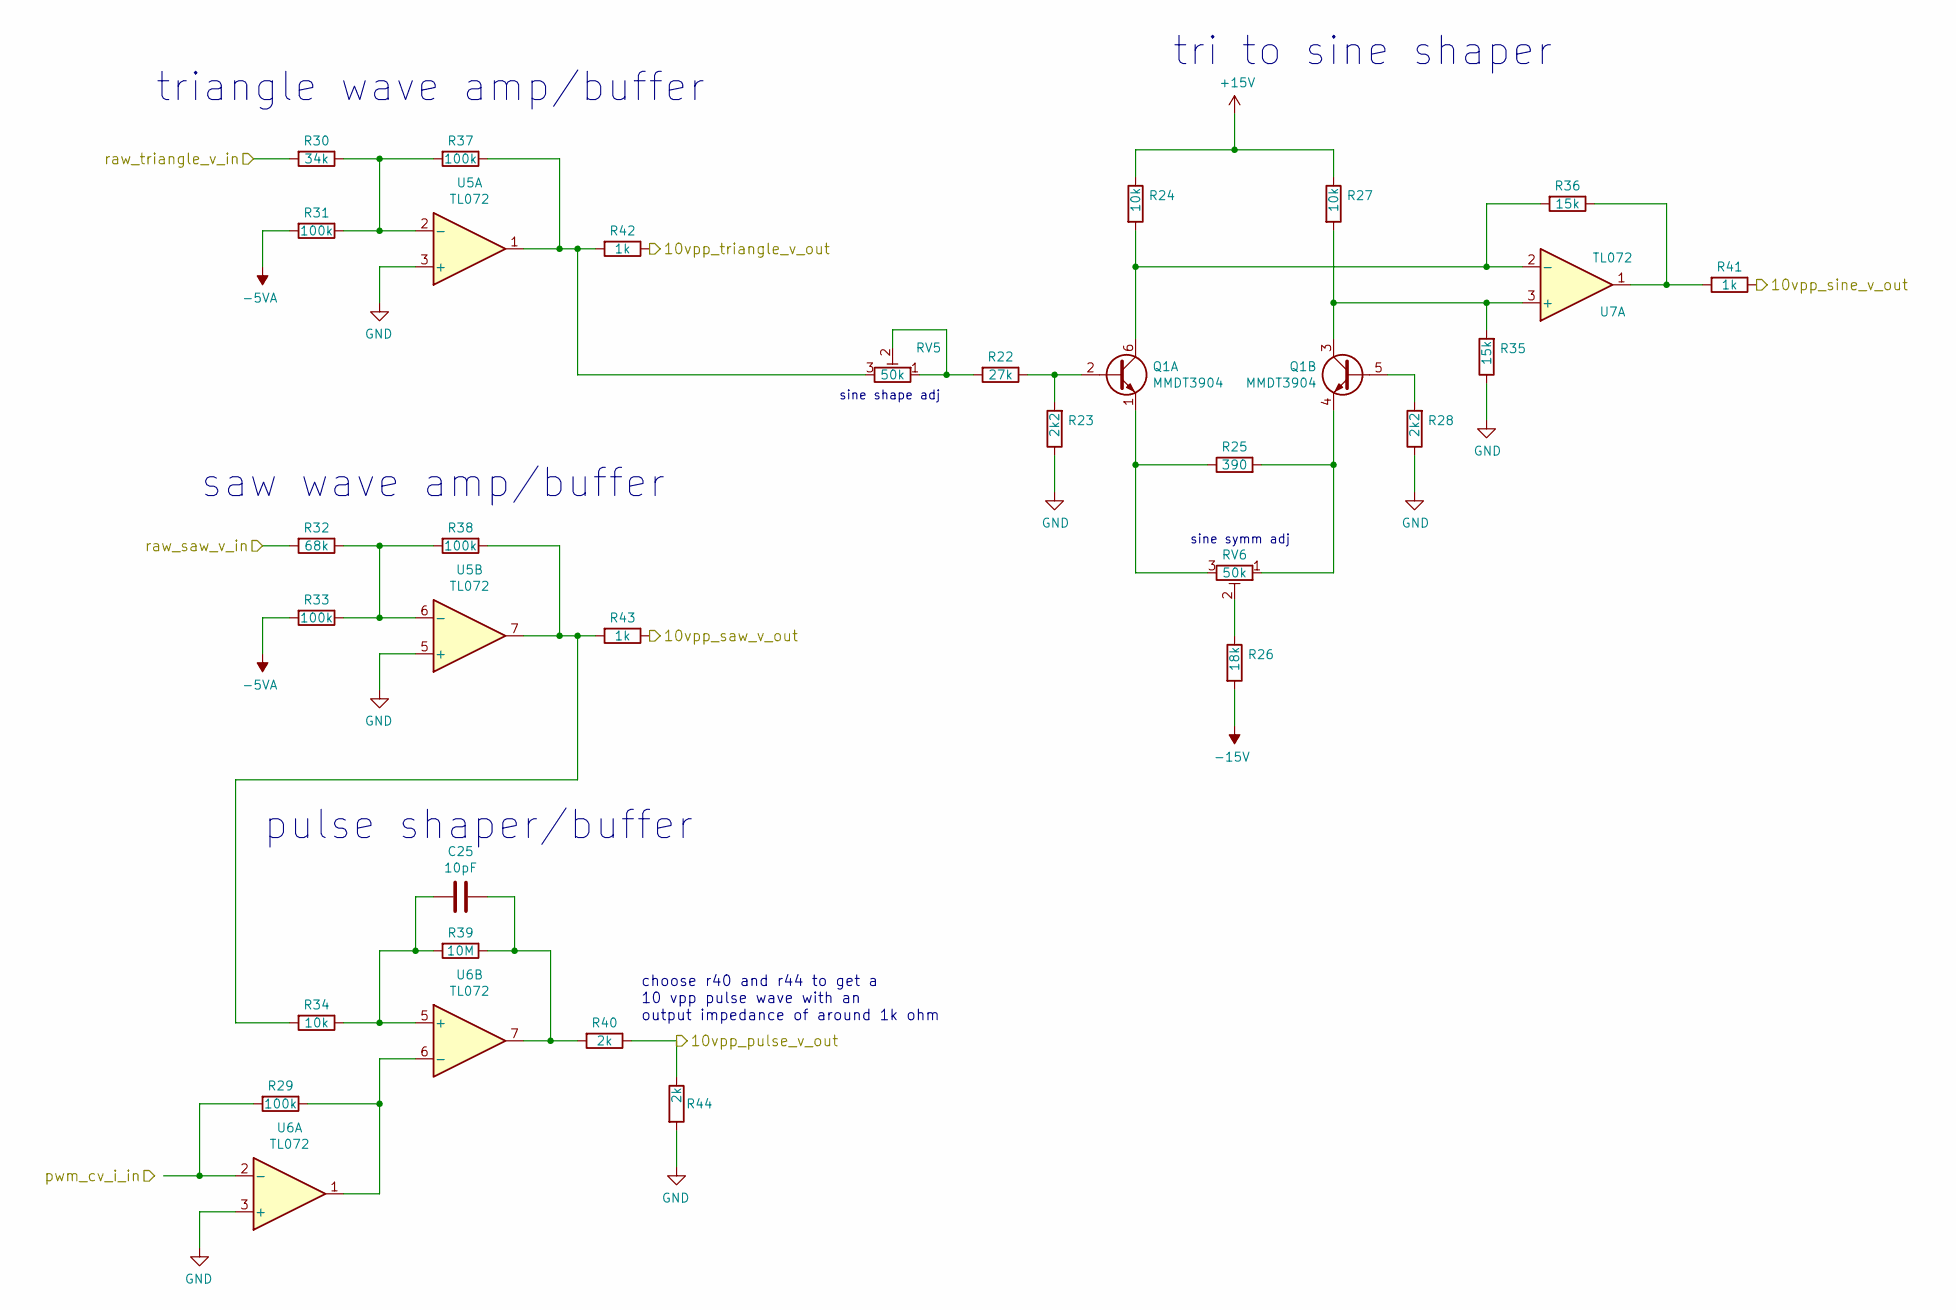
[picture p155: schematic Waveshapers.sch, CEM3340 VCO Waveshapers]

Parts:
C25: 10pF; C_0805_2012Metric_Pad1.15x1.40mm_HandSolder
Q1: MMDT3904; SOT-363_SC-70-6_Handsoldering
R22: 27k; R_0805_2012Metric_Pad1.15x1.40mm_HandSolder
R23, R28: 2k2; R_0805_2012Metric_Pad1.15x1.40mm_HandSolder
R24, R27, R34: 10k; R_0805_2012Metric_Pad1.15x1.40mm_HandSolder
R25: 390; R_0805_2012Metric_Pad1.15x1.40mm_HandSolder
R26: 18k; R_0805_2012Metric_Pad1.15x1.40mm_HandSolder
R29, R31, R33, R37, R38: 100k; R_0805_2012Metric_Pad1.15x1.40mm_HandSolder
R30: 34k; R_0805_2012Metric_Pad1.15x1.40mm_HandSolder
R32: 68k; R_0805_2012Metric_Pad1.15x1.40mm_HandSolder
R35, R36: 15k; R_0805_2012Metric_Pad1.15x1.40mm_HandSolder
R39: 10M; R_0805_2012Metric_Pad1.15x1.40mm_HandSolder
R40, R44: 2k; R_0805_2012Metric_Pad1.15x1.40mm_HandSolder
R41, R42, R43: 1k; R_0805_2012Metric_Pad1.15x1.40mm_HandSolder
RV5, RV6: 50k; Potentiometer_Bourns_3296W_Vertical
U5, U6, U7: TL072; SOIC-8_3.9x4.9mm_P1.27mm

Connections:
+15V: R24.1, R27.1; also elsewhere on the board
-5VA: R31.2, R33.2; also elsewhere on the board
-15V: R26.2; also elsewhere on the board
/Waveshapers/10vpp_pulse_v_out: R40.1, R44.1; also elsewhere on the board
/Waveshapers/10vpp_saw_v_out: R43.1; also elsewhere on the board
/Waveshapers/10vpp_sine_v_out: R41.1; also elsewhere on the board
/Waveshapers/10vpp_triangle_v_out: R42.1; also elsewhere on the board
/Waveshapers/raw_saw_v_in: R32.2; also elsewhere on the board
/Waveshapers/raw_triangle_v_in: R30.2; also elsewhere on the board
GND: R23.1, R28.1, R35.1, R44.2, U5.3 (+), U5.5 (+), U6.3 (+); also elsewhere on the board
unnamed: C25.1, R39.1, R40.2, U6.7
unnamed: C25.2, R34.1, R39.2, U6.5 (+)
unnamed: Q1.1 (E1), R25.1, RV6.3
unnamed: Q1.2 (B1), R22.1, R23.2
unnamed: Q1.3 (C2), R27.2, R35.2, U7.3 (+)
unnamed: Q1.4 (E2), R25.2, RV6.1
unnamed: Q1.5 (B2), R28.2
unnamed: Q1.6 (C1), R24.2, R36.2, U7.2 (-)
unnamed: R22.2, RV5.1, RV5.2
unnamed: R26.1, RV6.2
unnamed: R29.1, U6.1, U6.6 (-)
unnamed: R29.2, U6.2 (-)
unnamed: R30.1, R31.1, R37.2, U5.2 (-)
unnamed: R32.1, R33.1, R38.2, U5.6 (-)
unnamed: R34.2, R38.1, R43.2, U5.7
unnamed: R36.1, R41.2, U7.1
unnamed: R37.1, R42.2, RV5.3, U5.1

Notes on the sheet:
sine shape adj
sine symm adj
tri to sine shaper
triangle wave amp/buffer
saw wave amp/buffer
pulse shaper/buffer
choose r40 and r44 to get a 10 vpp pulse wave with an output impedance of around 1k ohm

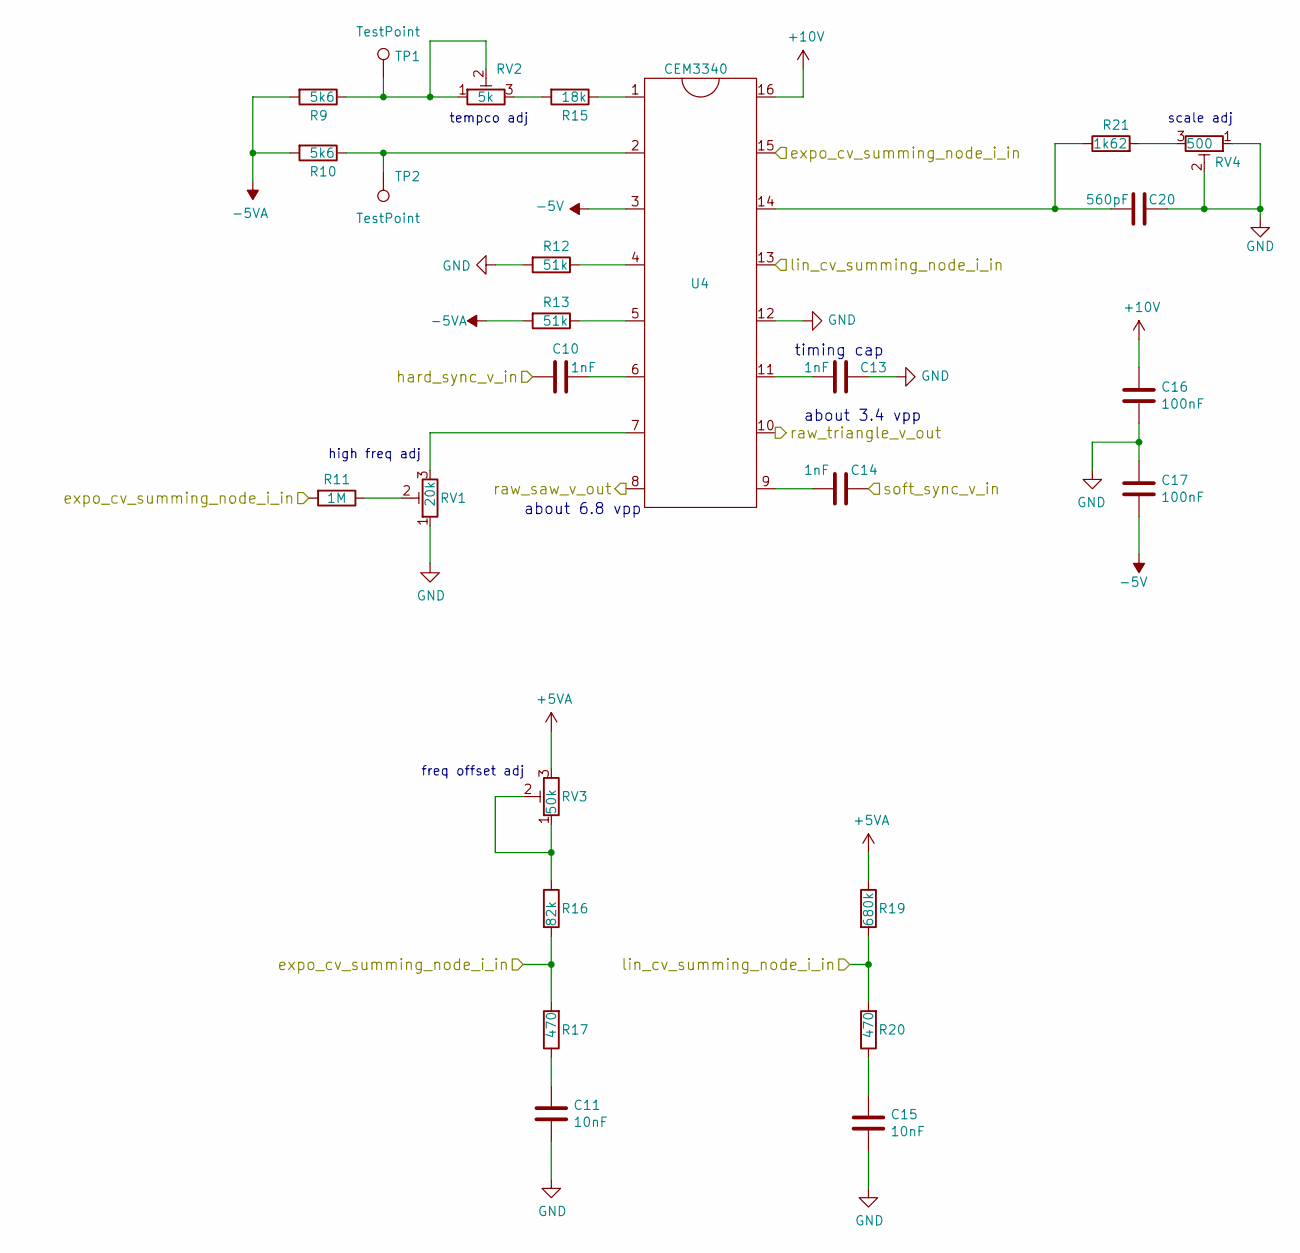
[picture p156: schematic VCO_Core.sch, CEM3340 VCO Core]

Parts:
C10, C13, C14: 1nF; C_0805_2012Metric_Pad1.15x1.40mm_HandSolder
C11, C15: 10nF; C_0805_2012Metric_Pad1.15x1.40mm_HandSolder
C16, C17: 100nF; C_0805_2012Metric_Pad1.15x1.40mm_HandSolder
C20: 560pF; C_0805_2012Metric_Pad1.15x1.40mm_HandSolder
R9, R10: 5k6; R_0805_2012Metric_Pad1.15x1.40mm_HandSolder
R11: 1M; R_0805_2012Metric_Pad1.15x1.40mm_HandSolder
R12, R13: 51k; R_0805_2012Metric_Pad1.15x1.40mm_HandSolder
R15: 18k; R_0805_2012Metric_Pad1.15x1.40mm_HandSolder
R16: 82k; R_0805_2012Metric_Pad1.15x1.40mm_HandSolder
R17, R20: 470; R_0805_2012Metric_Pad1.15x1.40mm_HandSolder
R19: 680k; R_0805_2012Metric_Pad1.15x1.40mm_HandSolder
R21: 1k62; R_0805_2012Metric_Pad1.15x1.40mm_HandSolder
RV1: 20k; Potentiometer_Bourns_3296W_Vertical
RV2: 5k; Potentiometer_Bourns_3296W_Vertical
RV3: 50k; Potentiometer_Bourns_3296W_Vertical
RV4: 500; Potentiometer_Bourns_3296W_Vertical
TP1, TP2: TestPoint; TestPoint_Keystone_5000-5004_Miniature
U4: CEM3340; DIP-16_W7.62mm

Connections:
+5VA: R19.1, RV3.3; also elsewhere on the board
+10V: C16.1, U4.16; also elsewhere on the board
-5V: C17.2, U4.3; also elsewhere on the board
-5VA: R9.2, R10.2, R13.2; also elsewhere on the board
/Signal_Inputs/expo_cv_i_out: R11.2, R16.2, R17.2, U4.15; also elsewhere on the board
/Signal_Inputs/lin_cv_i_out: R19.2, R20.2, U4.13; also elsewhere on the board
/VCO_Core/hard_sync_v_in: C10.2; also elsewhere on the board
/VCO_Core/soft_sync_v_in: C14.1; also elsewhere on the board
/Waveshapers/raw_saw_v_in: U4.8; also elsewhere on the board
/Waveshapers/raw_triangle_v_in: U4.10; also elsewhere on the board
GND: C11.2, C13.1, C15.2, C16.2, C17.1, C20.2, R12.2, RV1.1, RV4.1, RV4.2, U4.12; also elsewhere on the board
unnamed: C10.1, U4.6
unnamed: C11.1, R17.1
unnamed: C13.2, U4.11
unnamed: C14.2, U4.9
unnamed: C15.1, R20.1
unnamed: C20.1, R21.1, U4.14
unnamed: R9.1, RV2.1, RV2.2, TP1.1
unnamed: R10.1, TP2.1, U4.2
unnamed: R11.1, RV1.2
unnamed: R12.1, U4.4
unnamed: R13.1, U4.5
unnamed: R15.1, U4.1
unnamed: R15.2, RV2.3
unnamed: R16.1, RV3.1, RV3.2
unnamed: R21.2, RV4.3
unnamed: RV1.3, U4.7

Notes on the sheet:
tempco adj
scale adj
freq offset adj
high freq adj
timing cap
about 3.4 vpp
about 6.8 vpp

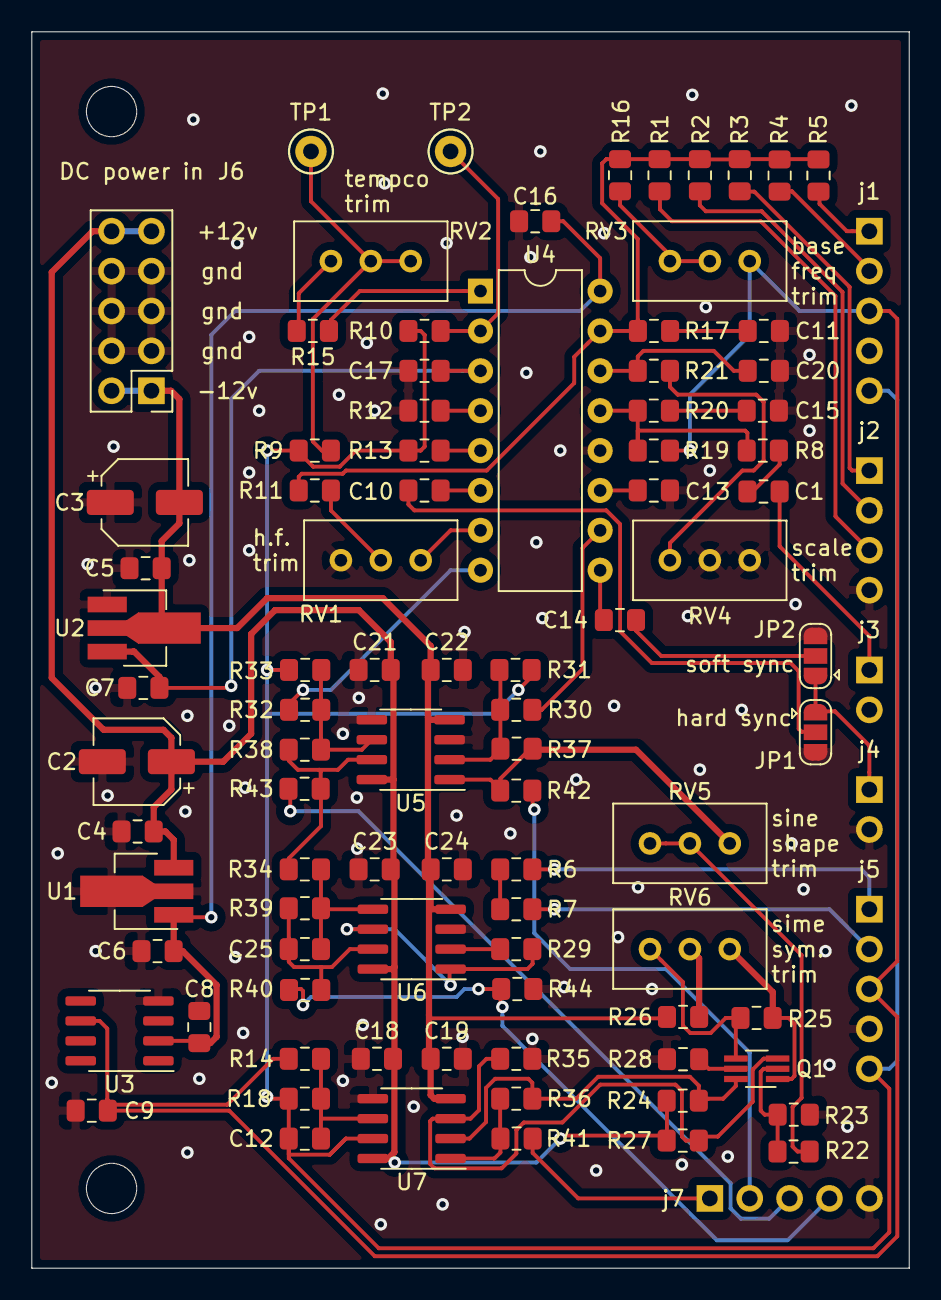
[picture p157: board CEM3340_VCO.kicad_pcb from above]

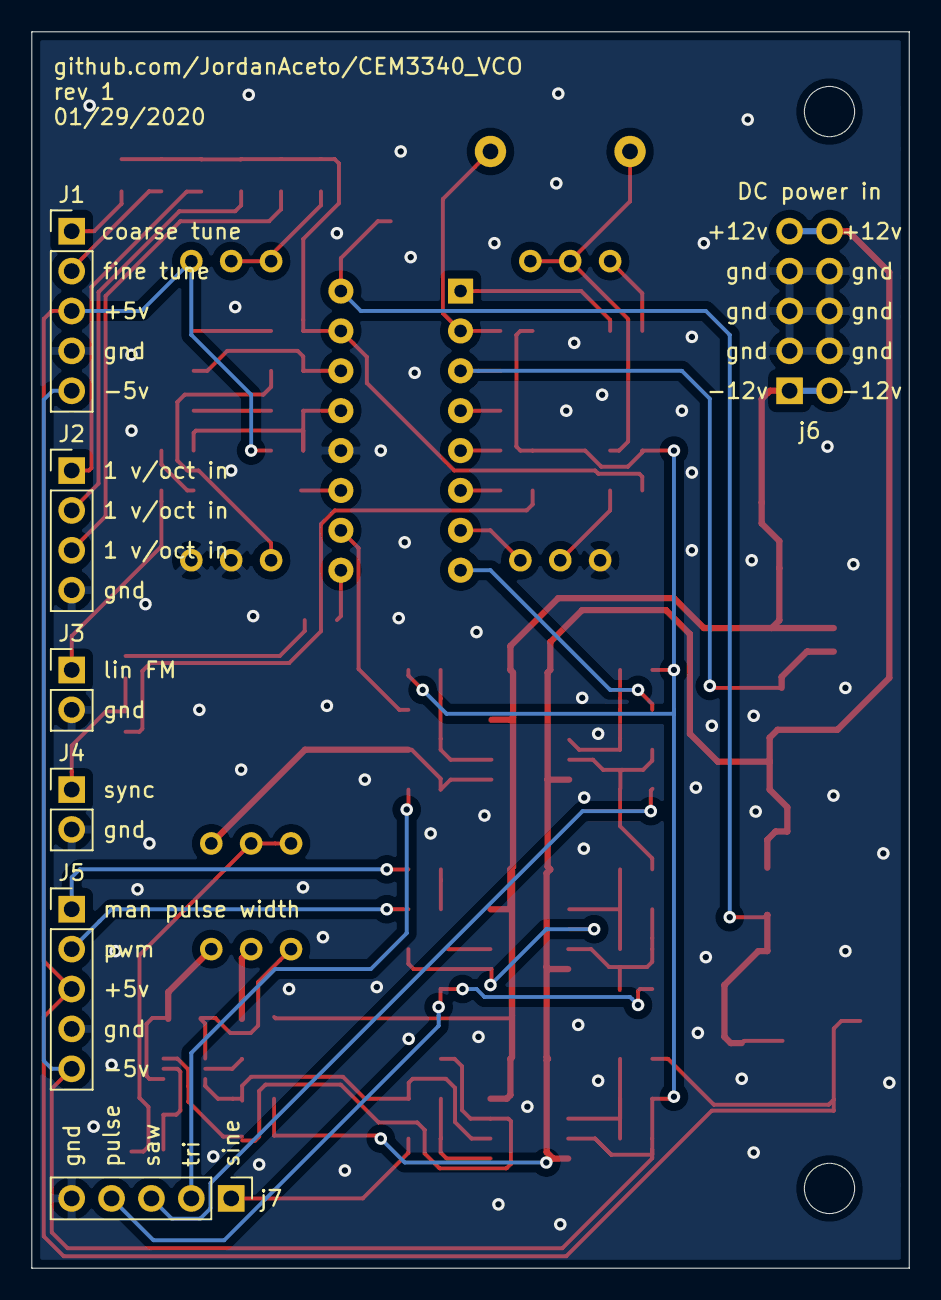
[picture p158: board CEM3340_VCO.kicad_pcb from below]

Board: 2 copper layers, 55.9 x 78.7 mm, 96 parts (6 on the bottom side), 62 nets.
